tascaenzo/8-bit-computer/docs/Specifica_IO_Video_CPU_8bit.docx

SPECIFICA TECNICA PRELIMINARE

Sottosistema I/O, tastiera PS/2, timer e video

CPU TTL a 8 bit con Tang Nano 9K

Stato: bozza architetturale

Versione: 0.2

Data: 22 agosto 2026

# 1. Scopo e perimetro

Questo documento definisce l'interfaccia preliminare fra la CPU TTL a 8 bit e una Tang Nano 9K. La FPGA svolge tre ruoli: memoria e generazione video HDMI, ricevitore e convertitore della tastiera PS/2, registri di I/O e timer. Il documento non definisce la microarchitettura interna della Control Unit né il set completo dei caratteri video.

Principio guida. La CPU mantiene un bus dati a 8 bit e un bus indirizzi a 16 bit; le periferiche sono osservate come registri memory-mapped. Le decisioni del programma passano attraverso registri, ALU e flag CPU. Nessun segnale periferico entra direttamente nella CU nella prima revisione.

# 2. Architettura generale

La Tang Nano 9K è l'unico endpoint programmabile del sottosistema. Sul lato CPU decodifica lo spazio video e i registri I/O; sul lato esterno acquisisce il protocollo PS/2 e genera il segnale HDMI. Il firmware FPGA isola quindi la logica TTL dai dettagli elettrici e temporali delle due interfacce.

Blocco | Responsabilità | Interfaccia verso CPU
CPU TTL | Esegue il programma e legge/scrive memoria e registri. | A[15:0], D[7:0], /RD, /WR, clock di sistema.
Tang Nano 9K | Decodifica, VRAM, video HDMI, ricezione PS/2, timer e registri. | Driver tri-state sul bus dati solo durante una lettura selezionata.
Tastiera PS/2 | Invia scan code seriali e clock generato dal dispositivo. | Due linee open-collector: DATA e CLK.
Uscita HDMI | Trasporta il flusso video prodotto dalla FPGA. | Nessun accesso diretto dalla CPU.

# 3. Mappa preliminare dello spazio indirizzi

La revisione propone I/O memory-mapped: si usano le istruzioni già previste LDA e STA. Le istruzioni IN e OUT restano disponibili nella ISA, ma non sono necessarie per accedere ai registri qui definiti. Questa scelta evita un secondo meccanismo di selezione porte e consente al decoder FPGA di usare sempre l'indirizzo a 16 bit.

Intervallo | Uso | Note
0x0000–0x3FFF | RAM e/o ROM di sistema | Configurazione fisica da definire separatamente.
0x4000–0x7FFF | Memoria video | 16 KiB, selezione FPGA quando A15:A14 = 01.
0x8000–0xFEFF | Riservato | Espansioni future, RAM aggiuntiva o periferiche.
0xFF00–0xFF0F | Registri I/O FPGA | Tastiera, timer e controllo diagnostico.
0xFF10–0xFFFF | Riservato | Espansioni future.

Regola del bus dati. In lettura la FPGA abilita i propri buffer tri-state solo se /RD è attivo e l'indirizzo appartiene al proprio intervallo. In scrittura la CPU è l'unico pilota del bus e la FPGA cattura D[7:0] solo se /WR è attivo e l'indirizzo è selezionato.

# 4. Sottosistema video

La memoria video occupa 0x4000–0x7FFF. L'indirizzo fisico interno alla VRAM è formato da A[13:0]; i bit A15:A14 sono usati solo per selezionare il blocco video. Il byte scritto dalla CPU è un codice di cella, interpretabile come carattere oppure tile dal firmware FPGA.

Bit indirizzo CPU | Significato | Valore
A15:A14 | Selezione area video | 01
A13:A7 | Coordinata Y | 0–127
A6:A0 | Coordinata X | 0–127
D7:D0 | Codice della cella | 0x00–0xFF

L'organizzazione logica massima è 128 × 128 celle, pari a 16.384 byte. La modalità visibile iniziale può usare una finestra di 80 × 60 celle da 8 × 8 pixel in uscita 640 × 480; il resto della VRAM è fuori area visibile oppure disponibile per pagine, scrolling o usi futuri.

Accesso concorrente. La VRAM deve avere due porte logiche: una porta di scrittura CPU e una porta di lettura per il generatore video. Le scritture CPU entrano nel dominio di clock FPGA attraverso una cattura sincronizzata; il generatore HDMI non deve mai leggere il bus TTL direttamente.

# 5. Interfaccia elettrica e protocollo CPU–FPGA

Il clock della CPU a 1 kHz è molto lento rispetto alla logica FPGA. Non è necessario rallentare la FPGA: è sufficiente trattare ogni ciclo CPU come una transazione di bus e sincronizzare i segnali TTL nel dominio interno della Tang Nano 9K. Prima del collegamento definitivo va verificata la compatibilità delle tensioni di ogni pin; gli I/O della FPGA non devono ricevere livelli a 5 V se non sono dichiarati tolleranti nel datasheet e nella configurazione della scheda.

Segnale | Direzione | Funzione
A[15:0] | CPU → FPGA | Indirizzo della cella video o del registro I/O.
D[7:0] | Bidirezionale | Dati; la FPGA pilota il bus esclusivamente durante una lettura selezionata.
/RD | CPU → FPGA | Strobe di lettura attivo basso.
/WR | CPU → FPGA | Strobe di scrittura attivo basso.
CLK_CPU | CPU → FPGA | Riferimento per campionare transazioni; non è il clock HDMI.
FPGA_D_OE | FPGA → buffer | Abilita i buffer tri-state dati verso la CPU.

Nota hardware. È preferibile usare buffer bidirezionali/tri-state esterni compatibili con i livelli TTL e 3,3 V della Tang Nano 9K, e level shifter dove necessari. La direzione del bus deve essere controllata in modo che CPU e FPGA non possano pilotare D[7:0] contemporaneamente.

# 6. Tastiera PS/2 e conversione a 8 bit

La Tang Nano 9K riceve direttamente il flusso PS/2, ricostruisce gli 11 bit del frame (start, 8 bit dati LSB-first, parità dispari e stop) e valida il frame. Il firmware mantiene il contesto necessario per i prefissi PS/2, quindi consegna alla CPU un solo valore normalizzato a 8 bit per evento di pressione.

Registro | Indirizzo | Lettura / scrittura
KEY_DATA | 0xFF00 | Lettura: 0x00 se non esiste un evento; altrimenti codice tasto 0x01–0xFF. Una lettura con dato valido consuma l'evento.
KEY_STATUS | 0xFF01 | Bit 0 READY; bit 1 OVERRUN; bit 2 PARITY_ERROR; bit 3 FRAME_ERROR; bit 7:4 riservati. Lettura non distruttiva.
KEY_CTRL | 0xFF02 | Scrittura: bit 0 cancella OVERRUN; bit 1 cancella gli errori; altri bit riservati.

Nella prima revisione KEY_DATA è un buffer di un evento. Se arriva un nuovo evento quando READY è già a 1, il nuovo evento non sovrascrive il dato non letto: viene impostato OVERRUN e il firmware può scartare il nuovo evento. Una FIFO interna è una successiva estensione compatibile, senza cambiare l'interfaccia software di base.

Codifica proposta. Il convertitore emette codici interni a 8 bit, non i scan code PS/2 grezzi. La tabella iniziale copre caratteri stampabili, Enter, Backspace, Tab, Esc e frecce. I break code (F0) non generano un evento nella versione base; i prefissi extended (E0) servono soltanto a distinguere i tasti estesi nella tabella di conversione.

Livelli elettrici PS/2. DATA e CLK sono linee open-collector con pull-up tipicamente verso 5 V. Non vanno collegate direttamente a un pin FPGA non tollerante a 5 V: servono level shifting o uno stadio open-drain compatibile. Il firmware sincronizza entrambi gli ingressi e rileva il fronte di discesa di CLK dopo la sincronizzazione.

# 7. Timer

Il timer non richiede READY o ACK. È un contatore free-running che la CPU legge senza modificarlo. Per evitare letture incoerenti, il valore non deve provenire da un contatore ripple non sincronizzato: il contatore deve essere sincrono nel dominio CLK_CPU, oppure il suo valore deve essere catturato in un latch prima di essere esposto al bus.

Registro | Accesso e semantica
TIME_LO (0xFF04) | Lettura: restituisce il byte basso e cattura il byte alto nel latch.
TIME_HI (0xFF05) | Lettura: restituisce il byte alto catturato dall'ultima lettura TIME_LO.
TIME_STATUS (0xFF06) | Bit 0: timer attivo; gli altri bit sono riservati nella prima revisione.

## 7.1 Frequenza consigliata

La CPU esegue cicli a 1 kHz, cioè un ciclo ogni 1 ms. Un tick timer a 1 kHz non viene perso dal contatore: la differenza fra due letture conserva tutti gli incrementi. Tuttavia lascia soltanto un ciclo CPU per tick, rende più probabile leggere durante una transizione e con un timer a 8 bit farebbe rollover ogni 256 ms. Non è la scelta più comoda per il software di base.

Tick | Cicli CPU per tick | Rollover 8 bit | Valutazione
1 kHz (1 ms) | 1 | 256 ms | Troppo fine per riferimento generale; utile solo per misura breve.
100 Hz (10 ms) | 10 | 2,56 s | Scelta consigliata come tick di sistema iniziale.
10 Hz (100 ms) | 100 | 25,6 s | Buona per funzioni lente, ma poco precisa per temporizzazioni brevi.

Decisione proposta. Generare un clock-enable ogni dieci fronti di CLK_CPU e incrementare un contatore sincrono a 16 bit nella FPGA. Non serve un oscillatore separato se si desidera che il tempo di sistema segua il clock CPU; questa soluzione elimina il crossing di clock e, a 100 Hz, lascia dieci cicli CPU fra due tick. Il contatore a 16 bit ricomincia dopo 655,36 s, ma la sottrazione modulo 2¹⁶ fornisce intervalli corretti purché siano inferiori a 655,36 s.

Se il timer deve restare attivo a CPU ferma. Usare una sorgente di clock indipendente nella FPGA e un contatore nel suo dominio. In questo caso TIME_LO deve catturare un'istantanea atomica del contatore tramite un handshake o una sincronizzazione progettata esplicitamente. Il rischio non è perdere tick interni, ma leggere un valore incoerente se il crossing di clock è trattato in modo ingenuo.

# 8. Sequenze di accesso software

Il software legge i registri tramite LDA. I flag della CPU vengono aggiornati solo quando il programma usa la ALU o CMP; una lettura I/O non deve modificare i flag. Per verificare un dato o la scadenza di un intervallo, il valore viene trasferito agli operandi ALU e confrontato normalmente.

1. Lettura tastiera: leggere KEY_DATA. Il valore 0x00 indica nessun evento; un valore diverso da zero è un codice interno di tasto e l'evento è già stato consumato.
2. Lettura tempo atomica: leggere TIME_LO, poi TIME_HI; combinare i due byte in software se serve un confronto a 16 bit.
3. Misura intervallo: salvare una lettura precedente e sottrarla dalla lettura corrente con aritmetica modulo 2¹⁶. L'intervallo è valido se è minore del periodo di rollover del contatore.

# 9. Decisioni fissate e punti aperti

Voce | Stato | Decisione / lavoro residuo
Video | Fissata | VRAM da 16 KiB memory-mapped, codici cella a 8 bit, generazione HDMI nella Tang Nano 9K.
Tastiera | Fissata | PS/2 decodificato e convertito in codice interno a 8 bit nella FPGA; buffer a un evento con flag di errore.
Timer | Proposta | Contatore sincrono a 16 bit, tick da 10 ms derivato da CLK_CPU a 1 kHz; lettura atomica LO/HI.
Elettrica | Da verificare | Schema dei level shifter, buffer bus e tensioni effettive dei pin Tang Nano 9K.
Codici tasti | Da definire | Tabella completa PS/2 → codice interno a 8 bit e comportamento dei modificatori.
ISA | Da allineare | Confermare che I/O memory-mapped via LDA/STA sia la convenzione di questa revisione.

La scelta del timer a 100 Hz non comporta la perdita di tick: il contatore registra ogni incremento anche se la CPU legge più tardi. Il requisito essenziale è che il software calcoli le differenze fra campioni e che l'hardware renda atomica la lettura del valore a 16 bit.

Specifica preliminare • 22 agosto 2026 •

CPU TTL 8 bit | Specifica I/O e video
