tascaenzo/8-bit-computer/wiki/blog/README.md

# Appunti tecnici dai video

Questa sezione raccoglie articoli tecnici ricavati dalle trascrizioni dei video già presenti in `wiki/videos`.

La regola di questa sezione è: documentare solo gli argomenti già trattati nei video. Le parti future della CPU, come control unit completa, EEPROM del microcodice, registri completi, bus di controllo o ISA definitiva, verranno documentate quando saranno coperte dalla serie.

## Articoli

- [01 Panoramica CPU 8 Bit](./01-Panoramica_Cpu_8_Bit.md)
- [02 Bus Dati e Organizzazione della Board](./02-Bus_Dati_e_Organizzazione_della_Board.md)
- [03 Pull-Up, Pull-Down e Ingressi TTL](./03-Pull_Up_Pull_Down_e_Ingressi_TTL.md)
- [04 ALU: Operazione AND](./04-ALU_Operazione_AND.md)
- [05 Buffer Tri-State e Collegamento al Bus Dati](./05-Buffer_Tri_State_e_Collegamento_al_Bus_Dati.md)
- [06 ALU: Operazione OR](./06-ALU_Operazione_OR.md)
- [07 ALU: Operazioni XOR e NOR](./07-ALU_Operazioni_XOR_e_NOR.md)
- [08 ALU: Operazioni NAND, XNOR e NOT](./08-ALU_Operazioni_NAND_XNOR_e_NOT.md)
- [09 Somma Binaria, Half Adder e Full Adder](./09-Somma_Binaria_Half_Adder_e_Full_Adder.md)
- [10 Complemento a Due e Numeri con Segno](./10-Complemento_a_Due_e_Numeri_con_Segno.md)
- [11 ALU: Somma e Sottrazione con il 74283](./11-ALU_Somma_e_Sottrazione_con_il_74283.md)
- [12 Flag della CPU: Carry, Negative, Zero e Overflow](./12-Flag_Carry_Negative_Zero_Overflow.md)
- [13 Operazioni di Confronto: A Uguale B, A Minore di B, A Maggiore di B](./13-Operazioni_di_Confronto.md)
- [14 Codice Operazione dell'ALU](./14-Codice_Operazione_ALU.md)
- [15 Segnale di Clock](./15-Segnale_di_Clock.md)
- [16 Flip-Flop SR: una Cella di Memoria](./16-Flip_Flop_SR.md)
- [17 Flip-Flop D e Salvataggio sul Fronte di Clock](./17-Flip_Flop_D.md)
