tascaenzo/8-bit-computer/docs/isa.md

# ISA CPU 8-bit

Bozza della Instruction Set Architecture della CPU didattica a 8 bit.

Questa specifica descrive l'architettura visibile al software, la semantica delle istruzioni e la loro codifica macchina: CPU a 8 bit, architettura di Von Neumann, memoria unica per codice e dati, bus dati a 8 bit e bus indirizzi a 16 bit.

## Stato del documento

Questo documento e la sorgente di verita per la progettazione della ISA. La sintassi dei file `.asm`, le label e le direttive sono documentate separatamente nella [specifica del linguaggio assembly](assembly-language.md). La compilazione e l'utilizzo dello strumento sono descritti nel [README dell'assembler](../tools/assembler/README.md).

## Decisioni confermate

- La CPU usa architettura di Von Neumann.
- Codice e dati condividono la stessa memoria.
- Il data bus e a 8 bit.
- L'address bus e a 16 bit.
- Ogni istruzione inizia con un opcode a 8 bit.
- Le istruzioni possono occupare 1, 2 o 3 byte.
- Gli indirizzi a 16 bit sono salvati in memoria in ordine little-endian: prima byte basso, poi byte alto.
- La CPU dispone di 8 registri generali: `R0`...`R7`.
- I registri generali sono codificati con 3 bit.
- La ALU usa due registri operando dedicati: `RA` e `RB`.
- Il registro `RA` contiene il primo operando della ALU e riceve anche il risultato dell'operazione.
- Il registro `RB` contiene il secondo operando della ALU.
- Il registro `RA` puo leggere e scrivere sul bus dati; il registro `RB` viene usato come registro temporaneo in ingresso alla ALU.
- La CPU dispone di un registro indice `IDX` a 16 bit, diviso in parte bassa e parte alta.
- Le due meta di `IDX` possono essere caricate separatamente dal data bus a 8 bit.
- `PC`, `MAR` e `IDX` possono pilotare il bus indirizzi, uno alla volta, tramite un selettore a 2 bit.
- `IDX` e destinato agli indirizzi calcolati dinamicamente e, in prospettiva, agli accessi alla memoria video memory-mapped.
- Per usare i registri generali con la ALU servono istruzioni di trasferimento tra `R0`...`R7` e i registri `RA`/`RB`.
- Non e ammesso il trasferimento diretto `MOV Rx, Ry` tra due registri generali.
- La CPU espone i flag `C`, `Z`, `N`, `O`: carry/borrow, zero, negativo, overflow.
- La ALU genera i segnali di flag in base all'operazione selezionata.
- Il salvataggio dei flag nel registro flag e controllato dalla control unit durante il microcodice dell'istruzione.
- Le istruzioni ALU salvano i flag; le istruzioni di load, store, trasferimento, input/output e salto non salvano nuovi flag.
- I primi 3 bit dell'opcode identificano la macrocategoria dell'istruzione.
- I 5 bit bassi dell'opcode contengono informazioni interpretate in modo diverso in base alla macrocategoria.
- Il confronto viene fatto con una istruzione `CMP`: la logica cablata della ALU esegue internamente la sottrazione di confronto e produce i segnali di flag.
- Il salto condizionato e una istruzione successiva che legge i flag.

## Architettura di memoria

La CPU usa una architettura di Von Neumann:

- codice e dati condividono la stessa memoria;
- la memoria e indirizzata tramite un address bus a 16 bit;
- ogni locazione di memoria contiene 8 bit, quindi 1 byte;
- il data bus e largo 8 bit.

La memoria puo essere vista come una sequenza di byte:

```text
address         value
0x0000          byte
0b0000000000000000

0x0001          byte
0b0000000000000001

0x0002          byte
0b0000000000000010
...
0xFFFF          byte
0b1111111111111111
```

Anche se i chip fisici usati nei primi test possono avere meno linee indirizzo, la CPU viene progettata per lavorare con indirizzi a 16 bit.

## Registri di indirizzamento e fetch

Dalle trascrizioni risultano questi registri rilevanti per il formato istruzioni:

| Registro | Dimensione | Ruolo |
| --- | ---: | --- |
| `PC` | 16 bit | Program Counter, punta al prossimo byte da leggere |
| `MAR` | 16 bit | Memory Address Register, pilota l'address bus |
| `IDX` | 16 bit | Index Register, contiene un indirizzo calcolato dal software |
| `IR` | 8 bit | Instruction Register, contiene l'opcode |
| `MDR` | 8 bit | Memory Data Register, contiene dati letti/scritti in memoria |

`PC`, `MAR` e `IDX` sono registri a 16 bit. `MAR` e `IDX` vengono caricati dal
data bus a 8 bit e sono quindi divisi logicamente in parte bassa e parte alta.

Un selettore a 2 bit abilita una sola sorgente del bus indirizzi tra `PC`, `MAR`
e `IDX`; la quarta combinazione rimane disponibile. In questo modo la Control
Unit usa due segnali di selezione invece di tre segnali `output enable`
indipendenti.

## Index Register `IDX`

`IDX` permette al software di costruire dinamicamente un indirizzo a 16 bit e
usarlo per accedere alla memoria. Le sue uscite sono collegate al bus indirizzi,
mentre le parti `IDX_L` e `IDX_H` ricevono i dati dal bus a 8 bit e dispongono di
enable di caricamento separati.

L'uso previsto comprende buffer, tabelle e memoria video memory-mapped, dove
l'indirizzo da leggere o scrivere cambia durante l'esecuzione del programma.

`IDX` e ora gestito dalla ISA con tre istruzioni:

- `LDX addr16` (`0xD8`): carica prima `IDX_L`, poi `IDX_H` in little-endian;
- `LDAI Rn` (`0x50-0x57`): legge `RAM[IDX]` in `Rn`;
- `STAI Rn` (`0x58-0x5F`): scrive `Rn` in `RAM[IDX]`.

Gli accessi non incrementano automaticamente `IDX`: il registro mantiene il
proprio valore fino a una nuova `LDX` o al reset.

## Formato generale

Ogni istruzione inizia sempre con un opcode a 8 bit.

In base all'opcode, la CPU sa quanti byte aggiuntivi deve leggere durante la fase di fetch.

Sono previste tre categorie:

| Formato  | Byte totali | Struttura | Uso |
| --- | ---: | --- | --- |
| `IMP` | 1 | `opcode` | istruzioni senza operando |
| `IMM8` | 2 | `opcode immediate` | istruzioni con valore immediato a 8 bit |
| `ADDR16` | 3 | `opcode addr_low addr_high` | istruzioni con indirizzo di memoria a 16 bit |

Le istruzioni `ADDR16` occupano sempre 3 byte. Il primo byte e l'opcode, i due byte successivi sono l'indirizzo a 16 bit.

Istruzioni `ADDR16` della ISA v0.1:

| Categoria | Istruzioni | Uso dell'indirizzo |
| --- | --- | --- |
| memoria | `LDA Rn, addr16`, `STA Rn, addr16` | indirizzo della cella dati da leggere/scrivere |
| salti | `JMP`, `JZ`, `JNZ`, `JC`, `JNC`, `JN`, `JNN`, `JO`, `JNO` | nuovo valore del `PC` se il salto viene eseguito |

In binario:

```mermaid
flowchart LR
    subgraph IMP["IMP (1 byte)"]
        op1["opcode 8 bit"]
    end
    subgraph IMM8["IMM8 (2 byte)"]
        op2["opcode 8 bit"] --> imm["immediato 8 bit"]
    end
    subgraph ADDR16["ADDR16 (3 byte)"]
        op3["opcode 8 bit"] --> al["addr_low 8 bit<br/>indirizzo bit 7..0"] --> ah["addr_high 8 bit<br/>indirizzo bit 15..8"]
    end
```

Dove:

- `o` indica i bit dell'opcode;
- `i` indica i bit dell'immediato;
- `a` indica la parte bassa dell'indirizzo;
- `A` indica la parte alta dell'indirizzo.

## Ordine degli indirizzi

Per gli operandi a 16 bit si usa ordine little-endian:

```text
addr_low  = bit 7..0
addr_high = bit 15..8
```

Esempio:

```asm
LDA R0, 0x1234
```

viene codificata come:

```text
opcode 0x34 0x12
opcode 0b00110100 0b00010010
```

Questa scelta e coerente con il fatto che `MAR` viene caricato dal bus dati in due passaggi: prima la parte bassa, poi la parte alta.

## Registri visibili alle istruzioni

La CPU dispone di 8 registri generali:

```text
R0, R1, R2, R3, R4, R5, R6, R7
```

Servono 3 bit per selezionare un registro:

```text
2^3 = 8 registri
```

| Registro | Codice bin | Codice dec |
| --- | --- | ---: |
| `R0` | `0b000` | 0 |
| `R1` | `0b001` | 1 |
| `R2` | `0b010` | 2 |
| `R3` | `0b011` | 3 |
| `R4` | `0b100` | 4 |
| `R5` | `0b101` | 5 |
| `R6` | `0b110` | 6 |
| `R7` | `0b111` | 7 |

Oltre ai registri generali, la ALU usa due registri dedicati:

| Registro | Dimensione | Uso |
| --- | ---: | --- |
| `RA` | 8 bit | primo operando della ALU e destinazione del risultato |
| `RB` | 8 bit | secondo operando della ALU |

Il flusso operativo della ALU e:

```mermaid
flowchart LR
    RG1["Registro generale"] -->|"MOV RA, Rn"| RA
    RG2["Registro generale"] -->|"MOV RB, Rn"| RB
    RA -->|operando A| ALU
    RB -->|operando B| ALU
    ALU -->|risultato| RA
    RA -->|"MOV Rn, RA"| RG3["Registro generale"]
```

Questa scelta deriva dall'hardware gia costruito:

- `RA` e `RB` alimentano direttamente gli ingressi della ALU;
- l'uscita della ALU viene salvata nuovamente in `RA`;
- `RA` puo essere riportato sul bus dati tramite buffer;
- `RB` e un registro temporaneo usato come secondo ingresso della ALU;
- per copiare un valore tra due registri generali si passa da `RA`.

Esempio di copia tra registri generali:

```asm
MOV RA, R0   ; R0 -> RA
MOV R1, RA   ; RA -> R1
```

## Struttura dell'opcode

L'opcode e largo 8 bit.

La struttura scelta e:

```mermaid
flowchart LR
    subgraph Opcode["Opcode 8 bit"]
        direction LR
        ccc["ccc<br/>bit 7-5<br/>macrocategoria"] --> xxxxx["xxxxx<br/>bit 4-0<br/>campo dati"]
    end
```

Dove:

- `ccc` identifica la macrocategoria dell'istruzione;
- `xxxxx` e un campo dati interno all'opcode;
- il significato di `xxxxx` dipende dalla macrocategoria.

Questa struttura serve anche a semplificare l'hardware. La control unit puo decodificare principalmente i 3 bit alti per capire il tipo generale di istruzione. I bit bassi possono invece essere portati, tramite buffer dati, verso blocchi specifici come:

- selezione dei registri generali;
- codice operazione della ALU;
- selezione di condizioni di salto;
- sotto-operazioni della stessa macrocategoria.

In questo modo non serve generare tutte queste informazioni come uscite separate della control unit: una parte del lavoro viene codificata direttamente dentro l'opcode.

## Macrocategorie

Mappa dei 3 bit alti dell'opcode, in ordine binario:

| Bit `ccc` | Hex range | Macrocategoria | Uso |
| --- | --- | --- | --- |
| `000` | `0x00-0x1F` | sistema / controllo | `NOP`, `HLT`, istruzioni senza operando speciale  |
| `001` | `0x20-0x3F` | load immediate | caricamento immediato in registro; `JO=0x30` |
| `010` | `0x40-0x5F` | memoria | load/store tra memoria e registri |
| `011` | `0x60-0x7F` | ALU | operazioni aritmetico-logiche |
| `100` | `0x80-0x9F` | I/O | lettura input e scrittura output |
| `101` | `0xA0-0xBF` | jump | `JMP`, `JNO`, `JZ`, `JNZ` |
| `110` | `0xC0-0xDF` | trasferimenti | passaggio dati tra registri generali, `RA` e `RB` |
| `111` | `0xE0-0xFF` | jump | `JC`, `JNC`, `JN`, `JNN` |

La regola generale e:

```text
ccc   = macrocategoria
xxxxx = campo interno riusabile
```

Le sottocategorie sono documentate sotto mantenendo lo stesso ordine binario di `ccc`: `000`, `001`, `010`, `011`, `100`, `101`, `110`, `111`.

## Campi comuni

Per le istruzioni che lavorano su un registro, i 3 bit bassi dell'opcode codificano il registro.

Schema:

```mermaid
flowchart LR
    subgraph Opcode["Opcode 8 bit"]
        direction LR
        ccc["ccc<br/>bit 7-5<br/>macrocategoria"] --> ss["ss<br/>bit 4-3<br/>sotto-operazione"] --> rrr["rrr<br/>bit 2-0<br/>registro"]
    end
```

Dove:

- `ccc` identifica la macrocategoria;
- `ss` e un sotto-campo dipendente dalla categoria;
- `rrr` identifica il registro `R0`...`R7`.

I bit `rrr`, cioe `IR[2:0]`, possono essere collegati tramite buffer alla logica di selezione dei registri generali.

Esempio:

| Istruzione | Opcode hex | Opcode bin |
| --- | ---: | --- |
| `LDI R0, imm8` | `0x20` | `0b00100000` |
| `LDI R1, imm8` | `0x21` | `0b00100001` |
| `LDI R2, imm8` | `0x22` | `0b00100010` |
| `LDI R3, imm8` | `0x23` | `0b00100011` |
| `LDI R4, imm8` | `0x24` | `0b00100100` |
| `LDI R5, imm8` | `0x25` | `0b00100101` |
| `LDI R6, imm8` | `0x26` | `0b00100110` |
| `LDI R7, imm8` | `0x27` | `0b00100111` |

In questo esempio:

```text
ccc = 001  load immediate
ss  = 00   sotto-operazione base
rrr = registro
```

### Codifica registri nel campo `rrr`

| Registro | `rrr` | Binario completo con base `xxxxx000` |
| --- | --- | --- |
| `R0` | `0b000` | `xxxxx000` |
| `R1` | `0b001` | `xxxxx001` |
| `R2` | `0b010` | `xxxxx010` |
| `R3` | `0b011` | `xxxxx011` |
| `R4` | `0b100` | `xxxxx100` |
| `R5` | `0b101` | `xxxxx101` |
| `R6` | `0b110` | `xxxxx110` |
| `R7` | `0b111` | `xxxxx111` |

## `ccc = 000` sistema / controllo

Range:

```text
0b00000000 - 0b00011111
0x00       - 0x1F
```

Sottocategorie:

| Opcode bin | Hex | Assembly  | Formato | Effetto |
| --- | ---: | --- | --- | --- |
| `0b00000000` | `0x00` | `HLT` | `IMP` | ferma la CPU |
| `0b00000001` | `0x01` | `NOP` | `IMP` | nessuna operazione |
| `0b00000010-0b00011111` | `0x02-0x1F` | riservata | - | espansioni future  |

Queste istruzioni non usano registri generali e non hanno operandi aggiuntivi.
Le Control ROM vedono solo `IR[7:3]`: `HLT` e `NOP` condividono quindi le
stesse uscite operative. ROM2 D6 (`SYS_STEP_n`) vale `0` solo in RUN/T2
per questo gruppo. La OR esterna fra `SYS_STEP_n` e `IR[2:0]` disabilita
il conteggio del microstep solo per HLT; per NOP il contatore prosegue
fino a `NEXT_FETCH`. Non interrompere direttamente il clock.

## `ccc = 001` load immediate

Range:

```text
0b00100000 - 0b00111111
0x20       - 0x3F
```

Schema:

```text
opcode = 001ssrrr
```

Sottocategorie:

| `ss` | Opcode bin | Hex range | Assembly | Formato | Effetto |
| ---- | --- | ---: | --- | --- | --- |
| `00` | `0b00100rrr` | `0x20-0x27` | `LDI Rn, imm8` | `IMM8`  | carica un valore immediato a 8 bit in `Rn` |
| `01` | `0b00101rrr` | `0x28-0x2F` | riservata | - | espansioni future |
| `10` | `0b00110rrr` | `0x30-0x37` | `JO` solo a `0x30` | `ADDR16` | salto se overflow; `0x31..0x37` riservati |
| `11` | `0b00111rrr` | `0x38-0x3F` | riservata | - | espansioni future |

Esempio:

```text
LDI R0, imm8 -> 0b00100000 -> 0x20
LDI R7, imm8 -> 0b00100111 -> 0x27
```

Tabella estesa `LDI`:

| Istruzione | Opcode hex | Opcode bin | Byte successivo |
| --- | ---: | --- | --- |
| `LDI R0, imm8` | `0x20` | `0b00100000` | `iiiiiiii` |
| `LDI R1, imm8` | `0x21` | `0b00100001` | `iiiiiiii` |
| `LDI R2, imm8` | `0x22` | `0b00100010` | `iiiiiiii` |
| `LDI R3, imm8` | `0x23` | `0b00100011` | `iiiiiiii` |
| `LDI R4, imm8` | `0x24` | `0b00100100` | `iiiiiiii` |
| `LDI R5, imm8` | `0x25` | `0b00100101` | `iiiiiiii` |
| `LDI R6, imm8` | `0x26` | `0b00100110` | `iiiiiiii` |
| `LDI R7, imm8` | `0x27` | `0b00100111` | `iiiiiiii` |

## `ccc = 010` memoria

Questa macrocategoria contiene istruzioni che accedono alla memoria tramite indirizzo assoluto a 16 bit.

Le istruzioni attive di questa categoria richiedono sempre un operando `addr16` e quindi occupano 3 byte:

```text
opcode addr_low addr_high
```

Range:

```text
0b01000000 - 0b01011111
0x40       - 0x5F
```

Schema:

```text
opcode = 010ssrrr
```

Sottocategorie:

| `ss` | Opcode bin | Hex range | Assembly | Formato  | Effetto |
| ---- | --- | ---: | --- | --- | --- |
| `00` | `0b01000rrr` | `0x40-0x47` | `LDA Rn, addr16` | `ADDR16` | carica in `Rn` il byte letto da memoria |
| `01` | `0b01001rrr` | `0x48-0x4F` | `STA Rn, addr16` | `ADDR16` | scrive `Rn` in memoria |
| `10` | `0b01010rrr` | `0x50-0x57` | `LDAI Rn` | `IMP` | carica `Rn` da `RAM[IDX]` |
| `11` | `0b01011rrr` | `0x58-0x5F` | `STAI Rn` | `IMP` | scrive `Rn` in `RAM[IDX]` |

Gli indirizzi `addr16` sono sempre codificati in little-endian:

```text
opcode addr_low addr_high
```

Esempio con `LDA R2, 0x1234`:

```text
opcode    = 0x42       = 0b01000010
addr_low  = 0x34       = 0b00110100
addr_high = 0x12       = 0b00010010
```

Tabella estesa `LDA`:

| Istruzione | Opcode hex | Opcode bin | Byte successivi |
| --- | ---: | --- | --- |
| `LDA R0, addr16` | `0x40` | `0b01000000` | `addr_low addr_high` |
| `LDA R1, addr16` | `0x41` | `0b01000001` | `addr_low addr_high` |
| `LDA R2, addr16` | `0x42` | `0b01000010` | `addr_low addr_high` |
| `LDA R3, addr16` | `0x43` | `0b01000011` | `addr_low addr_high` |
| `LDA R4, addr16` | `0x44` | `0b01000100` | `addr_low addr_high` |
| `LDA R5, addr16` | `0x45` | `0b01000101` | `addr_low addr_high` |
| `LDA R6, addr16` | `0x46` | `0b01000110` | `addr_low addr_high` |
| `LDA R7, addr16` | `0x47` | `0b01000111` | `addr_low addr_high` |

Tabella estesa `STA`:

| Istruzione | Opcode hex | Opcode bin | Byte successivi |
| --- | ---: | --- | --- |
| `STA R0, addr16` | `0x48` | `0b01001000` | `addr_low addr_high` |
| `STA R1, addr16` | `0x49` | `0b01001001` | `addr_low addr_high` |
| `STA R2, addr16` | `0x4A` | `0b01001010` | `addr_low addr_high` |
| `STA R3, addr16` | `0x4B` | `0b01001011` | `addr_low addr_high` |
| `STA R4, addr16` | `0x4C` | `0b01001100` | `addr_low addr_high` |
| `STA R5, addr16` | `0x4D` | `0b01001101` | `addr_low addr_high` |
| `STA R6, addr16` | `0x4E` | `0b01001110` | `addr_low addr_high` |
| `STA R7, addr16` | `0x4F` | `0b01001111` | `addr_low addr_high` |

## `ccc = 011` ALU

Range:

```text
0b01100000 - 0b01111111
0x60       - 0x7F
```

Per la macrocategoria ALU, i bit bassi dell'opcode possono essere usati per portare direttamente alla ALU il codice operazione.

Schema proposto:

```text
opcode = 011maaaa
```

Dove:

- `011` identifica una istruzione ALU;
- `m` e un bit di modo ancora da definire;
- `aaaa` e il codice operazione interno della ALU.

I bit `aaaa`, cioe `IR[3:0]`, possono essere collegati tramite buffer al decoder del codice operazione della ALU.

Sottocategorie:

| `m` | `aaaa` | Opcode bin | Hex | Assembly  | Formato | Effetto |
| --- | --- | --- | ---: | --- | --- | --- |
| `0` | `0000` | `0b01100000` | `0x60` | `AND` | `IMP` | `RA = RA AND RB` |
| `0` | `0001` | `0b01100001` | `0x61` | `OR` | `IMP` | `RA = RA OR RB` |
| `0` | `0010` | `0b01100010` | `0x62` | `XOR` | `IMP` | `RA = RA XOR RB` |
| `0` | `0011` | `0b01100011` | `0x63` | `NOR` | `IMP` | `RA = RA NOR RB` |
| `0` | `0100` | `0b01100100` | `0x64` | `NAND` | `IMP` | `RA = RA NAND RB` |
| `0` | `0101` | `0b01100101` | `0x65` | `XNOR` | `IMP` | `RA = RA XNOR RB` |
| `0` | `0110` | `0b01100110` | `0x66` | `NOT` | `IMP` | `RA = NOT RA` |
| `0` | `0111` | `0b01100111` | `0x67` | `ADD` | `IMP` | `RA = RA + RB` |
| `1` | `1000` | `0b01111000` | `0x78` | `SUB` | `IMP` | `RA = RA - RB` |
| `0` | `1001` | `0b01101001` | `0x69` | `CMP` | `IMP` | confronto cablato nella ALU, salva i flag |
| `0` | `1000,1010-1111` | `0b01101000,0b01101010-0b01101111` | `0x68,0x6A-0x6F` | riservata | - | espansioni future |
| `1` | `0000-0111,1001-1111` | `0b01110000-0b01110111,0b01111001-0b01111111` | `0x70-0x77,0x79-0x7F` | riservata | - | espansioni future |

Le istruzioni ALU non selezionano direttamente un registro generale. Operano sui registri dedicati `RA` e `RB`.

Per le operazioni binarie:

```text
RA = RA op RB
```

Per `NOT`:

```text
RA = NOT RA
```

Per `CMP`:

```text
flag_signals = compare(RA, RB)
```

`CMP` seleziona la rete di confronto gia cablata nella ALU. La ALU esegue internamente la sottrazione necessaria al confronto e produce i segnali di flag. La control unit deve poi abilitare, nel microcodice di `CMP`, il salvataggio di questi segnali nel registro flag.

`CMP` non deve essere considerata una copia esplicita del risultato in un registro generale. Una eventuale istruzione di salto successiva legge il registro flag.

## Flag

La CPU usa quattro flag principali:

| Flag | Nome | Significato |
| ---- | --- | --- |
| `C`  | Carry / Borrow | riporto in somma oppure prestito in sottrazione/confronto  |
| `Z`  | Zero | il risultato e `0b00000000` |
| `N`  | Negative | il bit 7 del risultato e `1` |
| `O`  | Overflow | overflow aritmetico con numeri signed in complemento a due |

La ALU produce i segnali di flag. Il registro flag li memorizza solo quando la control unit abilita il caricamento dei flag.

Le istruzioni che devono salvare i flag nel registro flag sono:

- operazioni ALU: `AND`, `OR`, `XOR`, `NOR`, `NAND`, `XNOR`, `NOT`, `ADD`, `SUB`;
- confronto: `CMP`.

Le istruzioni che non devono salvare nuovi flag sono:

- `NOP`, `HLT`;
- `LDI`, `LDA`, `STA`;
- `MOV RA, Rn`, `MOV RB, Rn`, `MOV Rn, RA`;
- `IN`, `OUT`;
- tutti i salti.

Per le operazioni logiche:

```text
Z = 1 se il risultato e 0
N = bit 7 del risultato
C = 0
O = 0
```

Per `ADD`:

```text
RA = RA + RB
C = carry out unsigned
Z = 1 se RA e 0 dopo l'operazione
N = bit 7 di RA dopo l'operazione
O = overflow signed in complemento a due
```

Per `SUB`:

```text
RA = RA - RB
C = borrow unsigned
Z = 1 se RA e 0 dopo l'operazione
N = bit 7 di RA dopo l'operazione
O = overflow signed in complemento a due
```

Per `CMP`:

```text
la ALU seleziona l'operazione cablata di confronto
la logica di confronto equivale a valutare RA - RB
i segnali C, Z, N, O vengono prodotti dalla ALU
la control unit salva questi segnali nel registro flag
RA non viene modificato
RB non viene modificato
```

Con questa convenzione, dopo `CMP`:

- `Z = 1` indica `RA == RB`;
- `Z = 0` indica `RA != RB`;
- `C = 1` indica `RA < RB` in confronto unsigned;
- `C = 0` indica `RA >= RB` in confronto unsigned.

## `ccc = 100` input / output

La categoria `100` e usata per le istruzioni di I/O.

Range:

```text
0b10000000 - 0b10011111
0x80       - 0x9F
```

Schema proposto:

```text
opcode = 100ssrrr
```

Dove:

- `100` identifica una istruzione di I/O;
- `ss` identifica il tipo di I/O;
- `rrr` identifica il registro generale `R0`...`R7`.

Sottocategorie:

| `ss` | Opcode bin | Hex range | Assembly  | Formato | Effetto |
| ---- | --- | ---: | --- | --- | --- |
| `00` | `0b10000rrr` | `0x80-0x87` | `IN Rn` | `IMP` | copia il valore della periferica di input in `Rn` |
| `01` | `0b10001rrr` | `0x88-0x8F` | `OUT Rn`  | `IMP` | copia `Rn` nel registro/periferica di output |
| `10` | `0b10010rrr` | `0x90-0x97` | riservata | - | espansioni future |
| `11` | `0b10011rrr` | `0x98-0x9F` | riservata | - | espansioni future |

`IN` rappresenta l'input a 8 bit collegato al bus dati tramite buffer, come lo switch usato nei test hardware.

`OUT` rappresenta un registro o periferica di output a 8 bit.

Tabella estesa `IN`:

| Istruzione | Opcode hex | Opcode bin |
| --- | ---: | --- |
| `IN R0` | `0x80` | `0b10000000` |
| `IN R1` | `0x81` | `0b10000001` |
| `IN R2` | `0x82` | `0b10000010` |
| `IN R3` | `0x83` | `0b10000011` |
| `IN R4` | `0x84` | `0b10000100` |
| `IN R5` | `0x85` | `0b10000101` |
| `IN R6` | `0x86` | `0b10000110` |
| `IN R7` | `0x87` | `0b10000111` |

Tabella estesa `OUT`:

| Istruzione | Opcode hex | Opcode bin |
| --- | ---: | --- |
| `OUT R0` | `0x88` | `0b10001000` |
| `OUT R1` | `0x89` | `0b10001001` |
| `OUT R2` | `0x8A` | `0b10001010` |
| `OUT R3` | `0x8B` | `0b10001011` |
| `OUT R4` | `0x8C` | `0b10001100` |
| `OUT R5` | `0x8D` | `0b10001101` |
| `OUT R6` | `0x8E` | `0b10001110` |
| `OUT R7` | `0x8F` | `0b10001111` |

## `ccc = 101` salti

La categoria `101` e usata per i salti assoluti e condizionati.

Tutte le istruzioni attive di questa categoria richiedono un operando `addr16` e quindi occupano 3 byte:

```text
opcode addr_low addr_high
```

I nove opcode sono distribuiti in **nove gruppi distinti di `IR[7:3]`**.
Questa scelta permette alle tre Control ROM, che ricevono solo quei cinque bit,
di scegliere autonomamente la condizione di salto senza una quarta EEPROM.
I vecchi opcode `0xA1..0xA7` non sono compatibili: occorre riassemblare e
riprogrammare la EPROM del programma.

Tutti i salti usano un indirizzo a 16 bit in formato little-endian. L'indirizzo rappresenta il valore da caricare nel `PC` se il salto viene eseguito.

```text
opcode addr_low addr_high
```

Tabella condizioni:

| Mnemonic |  Opcode hex | Opcode bin | Condizione | Dopo `CMP` unsigned |
| --- | ---: | --- | --- | --- |
| `JMP addr16` | `0xA0` | `0b10100000` | sempre | - |
| `JZ addr16`  | `0xB0` | `0b10110000` | `Z = 1` | salta se `RA == RB` |
| `JNZ addr16` | `0xB8` | `0b10111000` | `Z = 0` | salta se `RA != RB` |
| `JC addr16`  | `0xE0` | `0b11100000` | `C = 1` | salta se `RA < RB`  |
| `JNC addr16` | `0xE8` | `0b11101000` | `C = 0` | salta se `RA >= RB` |
| `JN addr16`  | `0xF0` | `0b11110000` | `N = 1` | - |
| `JNN addr16` | `0xF8` | `0b11111000` | `N = 0` | - |
| `JO addr16`  | `0x30` | `0b00110000` | `O = 1` | - |
| `JNO addr16` | `0xA8` | `0b10101000` | `O = 0` | - |
| altri opcode | — | — | riservati | Non usarli come alias dei salti. |

Per confronti unsigned dopo `CMP`:

- `JZ` salta se `RA == RB`;
- `JNZ` salta se `RA != RB`;
- `JC` salta se `RA < RB`;
- `JNC` salta se `RA >= RB`.

## `ccc = 110` trasferimenti

Per usare la ALU con i registri generali servono istruzioni di trasferimento esplicite.

Range:

```text
0b11000000 - 0b11011111
0xC0       - 0xDF
```

Schema:

```text
opcode = 110ssrrr
```

Dove:

- `110` identifica una istruzione di trasferimento;
- `ss` identifica il tipo di trasferimento;
- `rrr` identifica il registro generale `R0`...`R7`.

Sottocategorie:

| `ss` | Opcode bin | Hex range | Assembly | Formato | Effetto |
| ---- | --- | ---: | --- | --- | --- |
| `00` | `0b11000rrr` | `0xC0-0xC7` | `MOV RA, Rn` | `IMP` | copia `Rn` in `RA` |
| `01` | `0b11001rrr` | `0xC8-0xCF` | `MOV RB, Rn` | `IMP` | copia `Rn` in `RB` |
| `10` | `0b11010rrr` | `0xD0-0xD7` | `MOV Rn, RA` | `IMP` | copia `RA` in `Rn` |
| `11` | `0b11011000` | `0xD8` | `LDX addr16` | `ADDR16` | carica IDX |
| `11` | `0b11011001-0b11011111` | `0xD9-0xDF` | riservata | - | espansioni future |

Queste istruzioni rispettano il circuito visto nei video:

- un registro generale selezionato puo mettere il proprio valore sul bus dati;
- `RA` o `RB` possono salvare il valore presente sul bus;
- solo `RA` puo essere usato per riportare il risultato della ALU sul bus dati;
- per scrivere un risultato in un registro generale si copia `RA` nel registro scelto.

Non esiste una istruzione hardware `MOV Rn, Rm` per copiare direttamente tra due registri generali. Il blocco dei registri generali consente di selezionare un solo registro alla volta per lettura o scrittura, quindi la copia deve passare da `RA`.

Esempio di copia tra registri generali:

```asm
MOV RA, R0
MOV R1, RA
```

Esempio di somma:

```asm
LDI R0, 10
LDI R1, 20
MOV RA, R0
MOV RB, R1
ADD
MOV R2, RA
```

Effetto:

```text
RA = R0
RB = R1
RA = RA + RB
R2 = RA
```

Tabella estesa `MOV RA, Rn`:

| Istruzione | Opcode hex | Opcode bin |
| --- | ---: | --- |
| `MOV RA, R0` | `0xC0` | `0b11000000` |
| `MOV RA, R1` | `0xC1` | `0b11000001` |
| `MOV RA, R2` | `0xC2` | `0b11000010` |
| `MOV RA, R3` | `0xC3` | `0b11000011` |
| `MOV RA, R4` | `0xC4` | `0b11000100` |
| `MOV RA, R5` | `0xC5` | `0b11000101` |
| `MOV RA, R6` | `0xC6` | `0b11000110` |
| `MOV RA, R7` | `0xC7` | `0b11000111` |

Tabella estesa `MOV RB, Rn`:

| Istruzione | Opcode hex | Opcode bin |
| --- | ---: | --- |
| `MOV RB, R0` | `0xC8` | `0b11001000` |
| `MOV RB, R1` | `0xC9` | `0b11001001` |
| `MOV RB, R2` | `0xCA` | `0b11001010` |
| `MOV RB, R3` | `0xCB` | `0b11001011` |
| `MOV RB, R4` | `0xCC` | `0b11001100` |
| `MOV RB, R5` | `0xCD` | `0b11001101` |
| `MOV RB, R6` | `0xCE` | `0b11001110` |
| `MOV RB, R7` | `0xCF` | `0b11001111` |

Tabella estesa `MOV Rn, RA`:

| Istruzione | Opcode hex | Opcode bin |
| --- | ---: | --- |
| `MOV R0, RA` | `0xD0` | `0b11010000` |
| `MOV R1, RA` | `0xD1` | `0b11010001` |
| `MOV R2, RA` | `0xD2` | `0b11010010` |
| `MOV R3, RA` | `0xD3` | `0b11010011` |
| `MOV R4, RA` | `0xD4` | `0b11010100` |
| `MOV R5, RA` | `0xD5` | `0b11010101` |
| `MOV R6, RA` | `0xD6` | `0b11010110` |
| `MOV R7, RA` | `0xD7` | `0b11010111` |

## `ccc = 111` salti condizionati

Range:

```text
0b11100000 - 0b11111111
0xE0       - 0xFF
```

I quattro gruppi da otto opcode di questo range sono usati da
`JC=0xE0`, `JNC=0xE8`, `JN=0xF0` e `JNN=0xF8`. Solo il primo byte di
ciascun gruppo e definito come istruzione; gli altri restano riservati.

Sottocategorie:

| Campo `xxxxx` | Opcode bin | Hex range | Uso |
| --- | --- | ---: | --- |
| `00000` | `0b11100000` | `0xE0` | `JC` |
| `01000` | `0b11101000` | `0xE8` | `JNC` |
| `10000` | `0b11110000` | `0xF0` | `JN` |
| `11000` | `0b11111000` | `0xF8` | `JNN` |

## Tabella opcode riassuntiva

La seguente tabella riassume gli opcode definiti, mantenendo l'ordine binario delle macrocategorie `ccc`.
Le tabelle estese delle singole istruzioni sono nelle sezioni precedenti, dove si vede il valore completo per ogni registro.
`IN` e `OUT` sono ancora **solo nel simulatore/assembler**: i segnali delle
periferiche non sono presenti nelle tre Control ROM e la prova fisica li esclude.

| Mnemonic |  Opcode hex | Opcode bin | Formato  | Byte | Descrizione |
| --- | ---: | --- | --- | ---: | --- |
| `HLT` | `0x00` | `0b00000000` | `IMP` | 1 | Ferma la CPU tramite logica esterna |
| `NOP` | `0x01` | `0b00000001` | `IMP` | 1 | Nessuna operazione |
| `LDI Rn, imm8` | `0x20-0x27` | `0b00100rrr` | `IMM8` | 2 | Carica un valore immediato nel registro `Rn` |
| `LDA Rn, addr16` | `0x40-0x47` | `0b01000rrr` | `ADDR16` | 3 | Carica in `Rn` il byte letto dalla memoria |
| `STA Rn, addr16` | `0x48-0x4F` | `0b01001rrr` | `ADDR16` | 3 | Scrive `Rn` in memoria |
| `LDAI Rn` | `0x50-0x57` | `0b01010rrr` | `IMP` | 1 | Carica `Rn` da `RAM[IDX]` |
| `STAI Rn` | `0x58-0x5F` | `0b01011rrr` | `IMP` | 1 | Scrive `Rn` in `RAM[IDX]` |
| `AND` | `0x60` | `0b01100000` | `IMP` | 1 | Seleziona operazione ALU `AND` |
| `OR` | `0x61` | `0b01100001` | `IMP` | 1 | Seleziona operazione ALU `OR` |
| `XOR` | `0x62` | `0b01100010` | `IMP` | 1 | Seleziona operazione ALU `XOR` |
| `NOR` | `0x63` | `0b01100011` | `IMP` | 1 | Seleziona operazione ALU `NOR` |
| `NAND` | `0x64` | `0b01100100` | `IMP` | 1 | Seleziona operazione ALU `NAND` |
| `XNOR` | `0x65` | `0b01100101` | `IMP` | 1 | Seleziona operazione ALU `XNOR` |
| `NOT` | `0x66` | `0b01100110` | `IMP` | 1 | Esegue `RA = NOT RA` |
| `ADD` | `0x67` | `0b01100111` | `IMP` | 1 | Esegue `RA = RA + RB` |
| `SUB` | `0x78` | `0b01111000` | `IMP` | 1 | Esegue `RA = RA - RB` |
| `CMP` | `0x69` | `0b01101001` | `IMP` | 1 | Confronta `RA` e `RB` tramite logica ALU cablata, salva i flag |
| `IN Rn` | `0x80-0x87` | `0b10000rrr` | `IMP` | 1 | Copia input in `Rn` |
| `OUT Rn` | `0x88-0x8F` | `0b10001rrr` | `IMP` | 1 | Copia `Rn` nel registro/periferica di output |
| `JMP addr16` | `0xA0` | `0b10100000` | `ADDR16` | 3 | Carica il PC con un nuovo indirizzo |
| `JZ addr16` | `0xB0` | `0b10110000` | `ADDR16` | 3 | Salta se il flag zero e attivo |
| `JNZ addr16` | `0xB8` | `0b10111000` | `ADDR16` | 3 | Salta se il flag zero non e attivo |
| `JC addr16` | `0xE0` | `0b11100000` | `ADDR16` | 3 | Salta se il flag carry/borrow e attivo |
| `JNC addr16` | `0xE8` | `0b11101000` | `ADDR16` | 3 | Salta se il flag carry/borrow non e attivo |
| `JN addr16` | `0xF0` | `0b11110000` | `ADDR16` | 3 | Salta se il flag negative e attivo |
| `JNN addr16` | `0xF8` | `0b11111000` | `ADDR16` | 3 | Salta se il flag negative non e attivo |
| `JO addr16` | `0x30` | `0b00110000` | `ADDR16` | 3 | Salta se il flag overflow e attivo |
| `JNO addr16` | `0xA8` | `0b10101000` | `ADDR16` | 3 | Salta se il flag overflow non e attivo |
| `MOV RA, Rn` | `0xC0-0xC7` | `0b11000rrr` | `IMP` | 1 | Copia `Rn` nel registro `RA` |
| `MOV RB, Rn` | `0xC8-0xCF` | `0b11001rrr` | `IMP` | 1 | Copia `Rn` nel registro `RB` |
| `MOV Rn, RA` | `0xD0-0xD7` | `0b11010rrr` | `IMP` | 1 | Copia `RA` nel registro `Rn` |
| `LDX addr16` | `0xD8` | `0b11011000` | `ADDR16` | 3 | Carica `IDX` in little-endian |

## Confronti e salti condizionati

Il confronto viene diviso in due momenti:

1. `CMP`, che seleziona la logica di confronto cablata nella ALU e fa salvare i flag alla control unit;
2. una eventuale istruzione di salto, che legge il registro flag e decide se modificare il `PC`.

Esempio:

```asm
CMP
JZ 0x0200
```

In questo caso `CMP` confronta `RA` e `RB`. La ALU produce i segnali di flag usando la logica cablata di confronto; la control unit li salva nel registro flag. L'istruzione successiva, `JZ 0x0200`, controlla il flag `Z` salvato e salta all'indirizzo `0x0200` solo se quel flag e attivo.

Questa scelta evita di creare molte istruzioni ALU diverse per ogni confronto. La ALU produce i segnali di flag; la control unit decide quando salvarli e poi li usa per eseguire o ignorare il salto condizionato.

## Esempio di programma

Assembly:

```asm
; carica 10 in R0 e ferma la CPU
LDI R0, 0x0A
HLT
```

Codifica proposta:

```text
hex: 0x20 0x0A 0x00
bin: 0b00100000 0b00001010 0b00000000
```

Layout in memoria:

| Indirizzo hex | Indirizzo bin | Valore hex | Valore bin | Significato |
| --- | --- | --- | --- | --- |
| `0x0000` | `0b0000000000000000` | `0x20` | `0b00100000` | opcode `LDI R0, imm8` |
| `0x0001` | `0b0000000000000001` | `0x0A` | `0b00001010` | immediato |
| `0x0002` | `0b0000000000000010` | `0x00` | `0b00000000` | opcode `HLT` |

## Esempio ALU con registri RA e RB

Assembly:

```asm
; R2 = R0 + R1
MOV RA, R0
MOV RB, R1
ADD
MOV R2, RA
```

Codifica proposta:

```text
hex: 0xC0 0xC9 0x67 0xD2
bin: 0b11000000 0b11001001 0b01100111 0b11010010
```

Layout in memoria:

| Indirizzo hex | Indirizzo bin | Valore hex | Valore bin | Significato |
| --- | --- | --- | --- | --- |
| `0x0000` | `0b0000000000000000` | `0xC0` | `0b11000000` | opcode `MOV RA, R0` |
| `0x0001` | `0b0000000000000001` | `0xC9` | `0b11001001` | opcode `MOV RB, R1` |
| `0x0002` | `0b0000000000000010` | `0x67` | `0b01100111` | opcode `ADD` |
| `0x0003` | `0b0000000000000011` | `0xD2` | `0b11010010` | opcode `MOV R2, RA` |

## Esempio con indirizzo a 16 bit

Assembly:

```asm
LDA R2, 0x1234
STA R2, 0x00FF
```

Codifica proposta:

```text
LDA R2, 0x1234
hex: 0x42 0x34 0x12
bin: 0b01000010 0b00110100 0b00010010

STA R2, 0x00FF
hex: 0x4A 0xFF 0x00
bin: 0b01001010 0b11111111 0b00000000
```

Layout in memoria:

| Indirizzo hex | Indirizzo bin | Valore hex | Valore bin | Significato |
| --- | --- | --- | --- | --- |
| `0x0000` | `0b0000000000000000` | `0x42` | `0b01000010` | opcode `LDA R2, addr16` |
| `0x0001` | `0b0000000000000001` | `0x34` | `0b00110100` | byte basso indirizzo `0x1234` |
| `0x0002` | `0b0000000000000010` | `0x12` | `0b00010010` | byte alto indirizzo `0x1234`  |
| `0x0003` | `0b0000000000000011` | `0x4A` | `0b01001010` | opcode `STA R2, addr16` |
| `0x0004` | `0b0000000000000100` | `0xFF` | `0b11111111` | byte basso indirizzo `0x00FF` |
| `0x0005` | `0b0000000000000101` | `0x00` | `0b00000000` | byte alto indirizzo `0x00FF`  |

## Punti ancora da decidere

- riserva definitiva dei gruppi opcode non usati (gli opcode attivi hanno gruppi CU distinti quando serve);
- eventuale uso del range riservato `0b11011rrr` nei trasferimenti;
- codifica delle istruzioni per caricare `IDX_L` e `IDX_H`;
- codifica e sintassi degli accessi indiretti tramite `[IDX]`;
- eventuale incremento automatico di `IDX` negli accessi sequenziali;
- eventuali estensioni per input/output aggiuntivi;
- eventuale supporto a confronti signed tramite combinazioni dei flag `N` e `O`.
