tascaenzo/8-bit-computer/tools/eeprom-programmer/at28c64-mega/at28c64-mega.ino

/*
 * AT28C64 programmer for Arduino Mega.
 *
 * The hardware-specific EEPROM bus code lives in EepromBus.*.
 * The serial command parser lives in SerialCommands.*.
 */

#include <Arduino.h>

#include "include/EepromBus.h"
#include "include/ProgrammerConfig.h"
#include "include/SerialCommands.h"

void setup()
{
    Serial.begin(SERIAL_BAUD);

    eepromBusBegin();

    Serial.println(F("Programmatore AT28C64 pronto"));
    serialCommandsPrintHelp();
}

void loop()
{
    serialCommandsHandleInput();
}
