tascaenzo/8-bit-computer/tools/cu-bytecode/config/control_signals.h

#ifndef CPU8_CONTROL_SIGNALS_CONFIG_H
#define CPU8_CONTROL_SIGNALS_CONFIG_H

/*
 * Interfaccia della configurazione fisica delle tre Control ROM AT28C64.
 * Definisce i pin simbolici, gli ingressi di indirizzo condivisi e la tabella
 * che associa ogni uscita D0..D7 a un segnale di controllo.
 */

#include "../include/microcode.h"

/*
 * Le costanti dei pin sono qui; la mappa delle uscite e in control_signals.c.
 */
/* Costanti simboliche per tutti i pin della AT28C64 DIP-28. */
enum
{
    CPU8_AT28C64_PIN_A12 = 1,
    CPU8_AT28C64_PIN_A7 = 2,
    CPU8_AT28C64_PIN_A6 = 3,
    CPU8_AT28C64_PIN_A5 = 4,
    CPU8_AT28C64_PIN_A4 = 5,
    CPU8_AT28C64_PIN_A3 = 6,
    CPU8_AT28C64_PIN_A2 = 7,
    CPU8_AT28C64_PIN_A1 = 8,
    CPU8_AT28C64_PIN_IO0 = 9,
    CPU8_AT28C64_PIN_IO1 = 10,
    CPU8_AT28C64_PIN_IO2 = 11,
    CPU8_AT28C64_PIN_GND = 12,
    CPU8_AT28C64_PIN_IO3 = 13,
    CPU8_AT28C64_PIN_IO4 = 14,
    CPU8_AT28C64_PIN_IO5 = 15,
    CPU8_AT28C64_PIN_IO6 = 16,
    CPU8_AT28C64_PIN_IO7 = 17,
    CPU8_AT28C64_PIN_CE = 18,
    CPU8_AT28C64_PIN_A10 = 19,
    CPU8_AT28C64_PIN_OE = 20,
    CPU8_AT28C64_PIN_A11 = 21,
    CPU8_AT28C64_PIN_A9 = 22,
    CPU8_AT28C64_PIN_A8 = 23,
    CPU8_AT28C64_PIN_A0 = 24,
    CPU8_AT28C64_PIN_WE = 25,
    CPU8_AT28C64_PIN_NC26 = 26,
    CPU8_AT28C64_PIN_NC27 = 27,
    CPU8_AT28C64_PIN_VCC = 28
};

/* Ingressi identici sulle tre Control ROM. */
enum
{
    CPU8_CONTROL_ROM_PIN_BOOT_RUN = CPU8_AT28C64_PIN_A12,
    CPU8_CONTROL_ROM_PIN_IR_7 = CPU8_AT28C64_PIN_A7,
    CPU8_CONTROL_ROM_PIN_IR_6 = CPU8_AT28C64_PIN_A6,
    CPU8_CONTROL_ROM_PIN_IR_5 = CPU8_AT28C64_PIN_A5,
    CPU8_CONTROL_ROM_PIN_IR_4 = CPU8_AT28C64_PIN_A4,
    CPU8_CONTROL_ROM_PIN_IR_3 = CPU8_AT28C64_PIN_A3,
    CPU8_CONTROL_ROM_PIN_USTEP_2 = CPU8_AT28C64_PIN_A2,
    CPU8_CONTROL_ROM_PIN_USTEP_1 = CPU8_AT28C64_PIN_A1,
    CPU8_CONTROL_ROM_PIN_FLAG_N = CPU8_AT28C64_PIN_A10,
    CPU8_CONTROL_ROM_PIN_FLAG_O = CPU8_AT28C64_PIN_A11,
    CPU8_CONTROL_ROM_PIN_FLAG_Z = CPU8_AT28C64_PIN_A9,
    CPU8_CONTROL_ROM_PIN_FLAG_C = CPU8_AT28C64_PIN_A8,
    CPU8_CONTROL_ROM_PIN_USTEP_0 = CPU8_AT28C64_PIN_A0,
    CPU8_CONTROL_ROM_PIN_CE = CPU8_AT28C64_PIN_CE,
    CPU8_CONTROL_ROM_PIN_OE = CPU8_AT28C64_PIN_OE,
    CPU8_CONTROL_ROM_PIN_WE = CPU8_AT28C64_PIN_WE,
    CPU8_CONTROL_ROM_PIN_GND = CPU8_AT28C64_PIN_GND,
    CPU8_CONTROL_ROM_PIN_VCC = CPU8_AT28C64_PIN_VCC,
    CPU8_CONTROL_ROM_PIN_NC26 = CPU8_AT28C64_PIN_NC26,
    CPU8_CONTROL_ROM_PIN_NC27 = CPU8_AT28C64_PIN_NC27,
    CPU8_CONTROL_ROM_PIN_D0 = CPU8_AT28C64_PIN_IO0,
    CPU8_CONTROL_ROM_PIN_D1 = CPU8_AT28C64_PIN_IO1,
    CPU8_CONTROL_ROM_PIN_D2 = CPU8_AT28C64_PIN_IO2,
    CPU8_CONTROL_ROM_PIN_D3 = CPU8_AT28C64_PIN_IO3,
    CPU8_CONTROL_ROM_PIN_D4 = CPU8_AT28C64_PIN_IO4,
    CPU8_CONTROL_ROM_PIN_D5 = CPU8_AT28C64_PIN_IO5,
    CPU8_CONTROL_ROM_PIN_D6 = CPU8_AT28C64_PIN_IO6,
    CPU8_CONTROL_ROM_PIN_D7 = CPU8_AT28C64_PIN_IO7
};

/* I 13 segnali che formano l'indirizzo, comuni alle tre Control ROM. */
typedef enum
{
    CTRL_EEPROM_ADDR_USTEP_0,
    CTRL_EEPROM_ADDR_USTEP_1,
    CTRL_EEPROM_ADDR_USTEP_2,
    CTRL_EEPROM_ADDR_IR_3,
    CTRL_EEPROM_ADDR_IR_4,
    CTRL_EEPROM_ADDR_IR_5,
    CTRL_EEPROM_ADDR_IR_6,
    CTRL_EEPROM_ADDR_IR_7,
    CTRL_EEPROM_ADDR_FLAG_C,
    CTRL_EEPROM_ADDR_FLAG_Z,
    CTRL_EEPROM_ADDR_FLAG_N,
    CTRL_EEPROM_ADDR_FLAG_O,
    CTRL_EEPROM_ADDR_BOOT_RUN
} ControlEepromAddressSignal;

typedef struct
{
    ControlEepromAddressSignal signal;
    uint8_t pin;
} ControlEepromAddressConfig;

extern const ControlEepromAddressConfig CPU8_CONTROL_EEPROM_ADDRESS_CONFIGS[];
extern const size_t CPU8_CONTROL_EEPROM_ADDRESS_CONFIG_COUNT;

extern const ControlSignalConfig CPU8_CONTROL_SIGNAL_CONFIGS[];
extern const size_t CPU8_CONTROL_SIGNAL_CONFIG_COUNT;

#endif
