tascaenzo/8-bit-computer/tools/eeprom-programmer/at28c64-mega/include/EepromBus.h

#ifndef CPU8_AT28C64_EEPROM_BUS_H
#define CPU8_AT28C64_EEPROM_BUS_H

#include <Arduino.h>

/* Inizializza pin indirizzo, dati e controllo in stato inattivo. */
void eepromBusBegin();

/* Legge un byte dalla EEPROM. Il chiamante deve passare un indirizzo valido. */
uint8_t eepromReadByte(uint16_t address);

/* Scrive un byte, attende il ciclo interno e lascia la verifica al chiamante. */
void eepromWriteByte(uint16_t address, uint8_t value);

/*
 * Scrive un byte usando la sequenza Software Data Protection della AT28C64B.
 * Serve per EEPROM che hanno la protezione software gia attiva.
 */
void eepromWriteByteProtected(uint16_t address, uint8_t value);

#endif
